mamut-tme/QuickJoy-M-5-SV-201/QuickJoy_M-5_SV-201.kicad_sch

## KiCad design QuickJoy_M-5_SV-201.kicad_sch (2022-11-13)

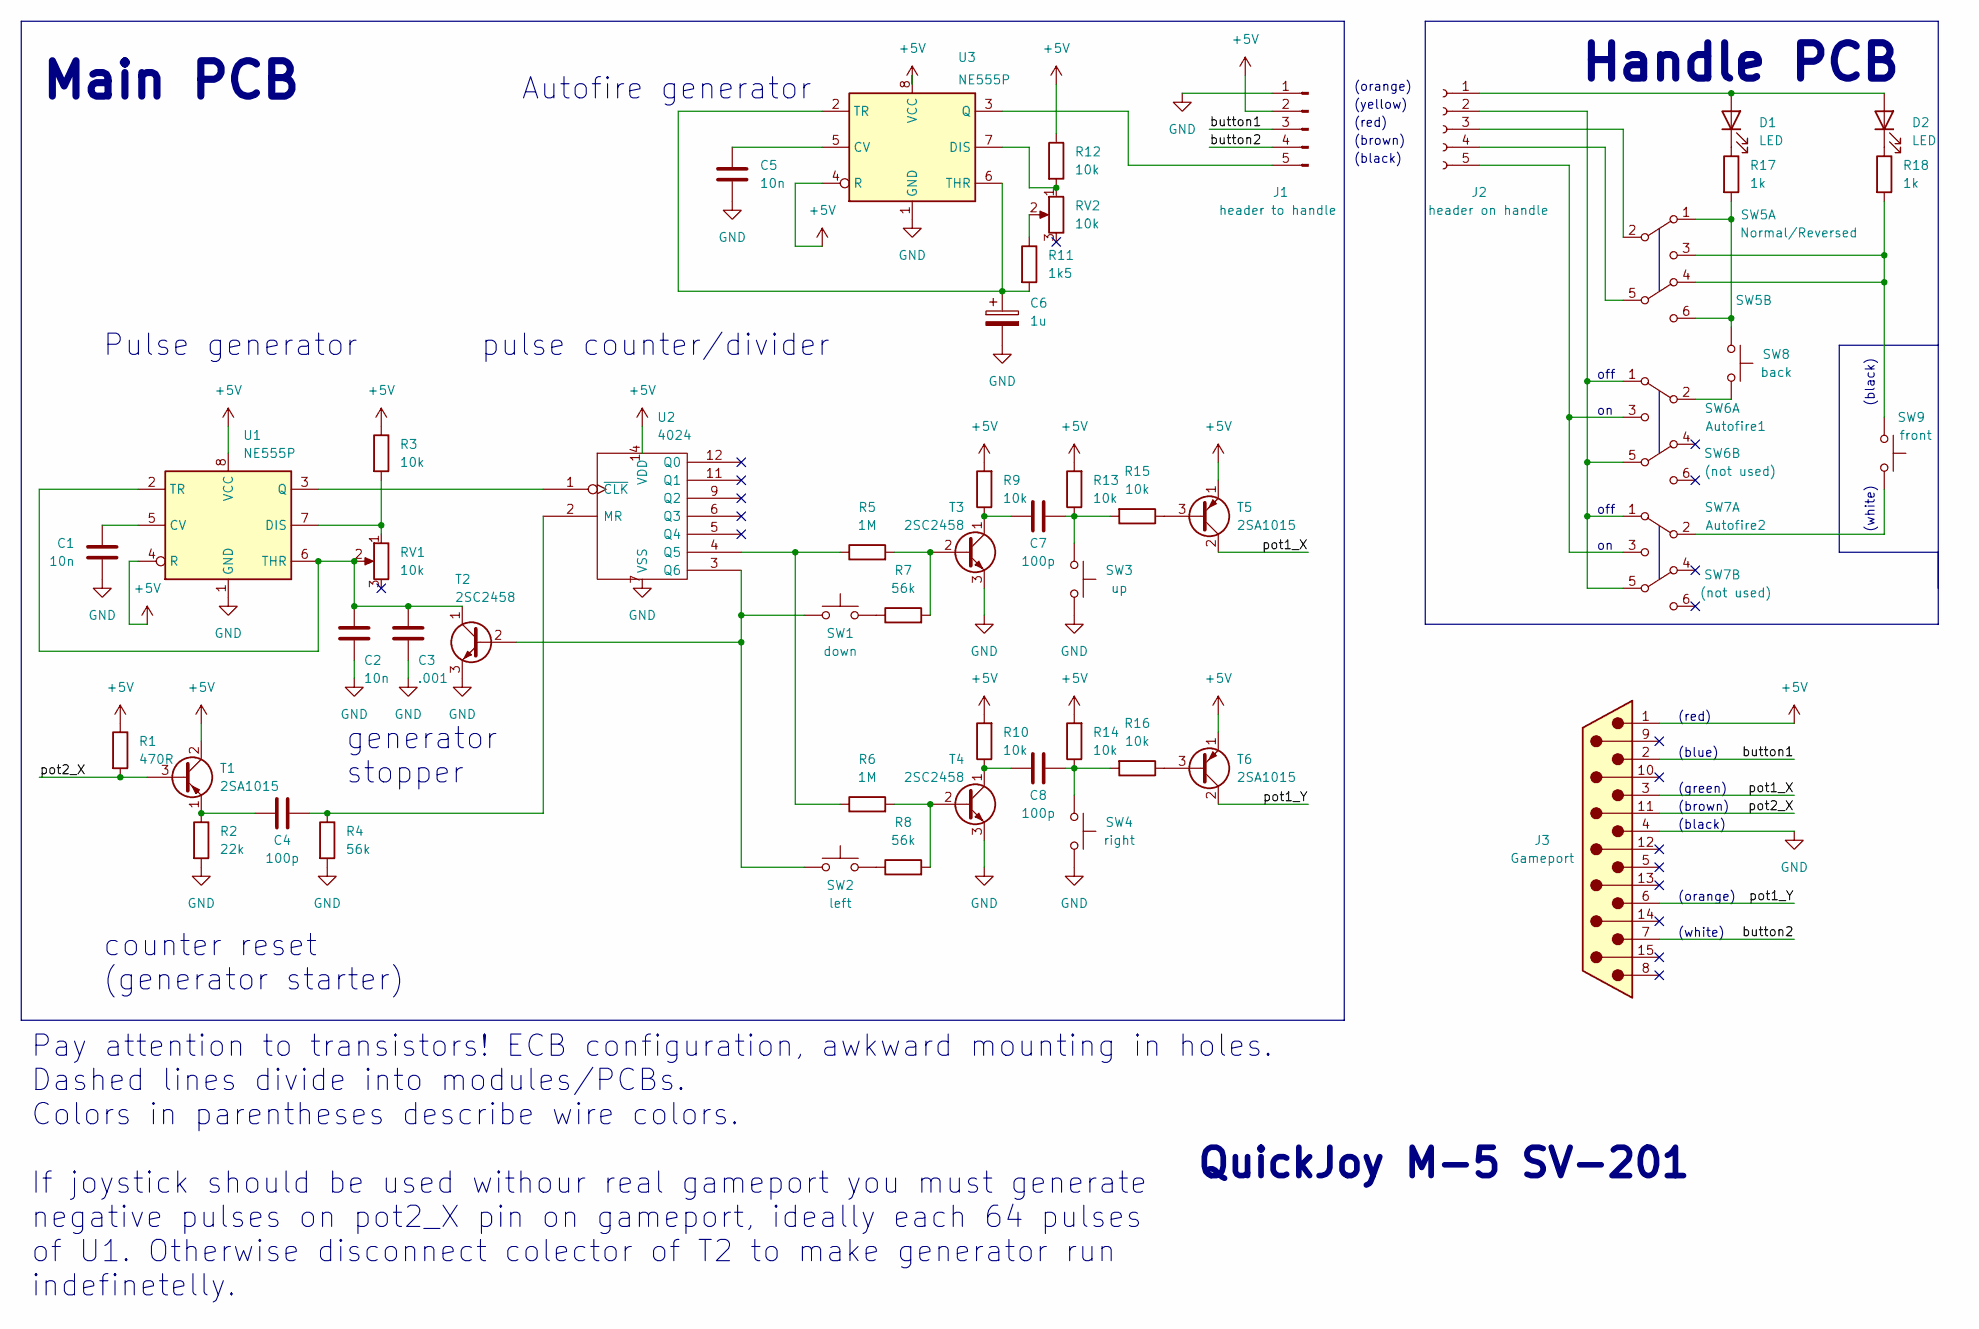
[picture p3: schematic QuickJoy_M-5_SV-201.kicad_sch]

Parts:
C1, C2, C5: 10n
C3: .001
C4, C7, C8: 100p
C6: 1u
D1, D2: LED
J1: header to handle
J2: header on handle
J3: Gameport
R1: 470R
R2: 22k
R3, R9, R10, R12, R13, R14, R15, R16: 10k
R4, R7, R8: 56k
R5, R6: 1M
R11: 1k5
R17, R18: 1k
RV1, RV2: 10k
SW1: down
SW2: left
SW3: up
SW4: right
SW5: Normal/Reversed
SW6: Autofire1
SW7: (not used)
SW8: back
SW9: front
T1, T5, T6: 2SA1015; TO-92_Inline
T2, T3, T4: 2SC2458; TO-92_Inline
U1, U3: NE555P; DIP-8_W7.62mm
U2: 4024

Connections:
+5V: J1.2, J3.1, R1.1, R3.1, R9.2, R10.2, R12.1, R13.2, R14.2, T1.2 (C), T5.1 (E), T6.1 (E), U1.4 (R), U1.8 (VCC), U2.14 (VDD), U3.4 (R), U3.8 (VCC)
GND: C1.2, C2.2, C3.2, C5.2, C6.2, J1.1, J3.4, R2.2, R4.2, SW3.3 (B), SW3.4 (B), SW4.3 (B), SW4.4 (B), T2.3 (E), T3.3 (E), T4.3 (E), U1.1 (GND), U2.7 (VSS), U3.1 (GND)
unnamed: C1.1, U1.5 (CV)
unnamed: C2.1, C3.1, RV1.2, T2.1 (C), U1.2 (TR), U1.6 (THR)
unnamed: C4.1, R2.1, T1.1 (E)
unnamed: C4.2, R4.1, U2.2 (MR)
unnamed: C5.1, U3.5 (CV)
unnamed: C6.1, R11.2, U3.2 (TR), U3.6 (THR)
unnamed: C7.1, R9.1, T3.1 (C)
unnamed: C7.2, R13.1, R15.2, SW3.1 (A), SW3.2 (A)
unnamed: C8.1, R10.1, T4.1 (C)
unnamed: C8.2, R14.1, R16.2, SW4.1 (A), SW4.2 (A)
unnamed: D1.1 (K), R17.1
unnamed: D1.2 (A), D2.2 (A), J2.1
unnamed: D2.1 (K), R18.1
unnamed: J1.5, U3.3 (Q)
unnamed: J2.2, SW6.1 (A), SW6.5 (B), SW7.1 (A), SW7.5 (B)
unnamed: J2.3, SW5.2 (B)
unnamed: J2.4, SW5.5 (B)
unnamed: J2.5, SW6.3 (C), SW7.3 (C)
unnamed: R3.2, RV1.1, U1.7 (DIS)
unnamed: R5.1, R6.1, U2.4 (Q5)
unnamed: R5.2, R7.2, T3.2 (B)
unnamed: R6.2, R8.2, T4.2 (B)
unnamed: R7.1, SW1.3 (B), SW1.4 (B)
unnamed: R8.1, SW2.3 (B), SW2.4 (B)
unnamed: R11.1, RV2.2
unnamed: R12.2, RV2.1, U3.7 (DIS)
unnamed: R15.1, T5.3 (B)
unnamed: R16.1, T6.3 (B)
unnamed: R17.2, SW5.1 (A), SW5.6 (C), SW8.1 (A), SW8.2 (A)
unnamed: R18.2, SW5.3 (C), SW5.4 (A), SW9.1 (A), SW9.2 (A)
unnamed: SW1.1 (A), SW1.2 (A), SW2.1 (A), SW2.2 (A), T2.2 (B), U2.3 (Q6)
unnamed: SW6.2 (B), SW8.3 (B), SW8.4 (B)
unnamed: SW7.2 (B), SW9.3 (B), SW9.4 (B)
unnamed: U1.3 (Q), U2.1 (~CLK)
button1: J1.3, J3.2
button2: J1.4, J3.7
pot1_X: J3.3, T5.2 (C)
pot1_Y: J3.6, T6.2 (C)
pot2_X: J3.11 (P111), R1.2, T1.3 (B)

Notes on the sheet:
(white)
off
(blue)
(yellow)
(black)
Pay attention to transistors! ECB configuration, awkward mounting in holes. Dashed lines divide into modules/PCBs. Colors in parentheses describe wire colors. If joystick should be used withour real gameport you must generate negative pulses on pot2_X pin on gameport, ideally each 64 pulses of U1. 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
(orange)
(brown)
pulse counter/divider
Main PCB
(green)
(red)
Pulse generator
Handle PCB
generator stopper
QuickJoy M-5 SV-201
Autofire generator
counter reset (generator starter)
